VivianKuKu/CASA0021_Group-Prototype_Thinking-Scents/flutterBleV7/arduino_secrets.h

// This is the header file to store the wifi config

#ifndef _ARDUINO_SECRETS_H    // Put these two lines at the top of your file.
#define _ARDUINO_SECRETS_H  // (Use a suitable name, usually based on the file name.)

// Place your main header code here.
//please enter your sensitive data in the Secret tab/arduino_secrets.h

//
//#define SECRET_SSID "McDonald"
//#define SECRET_PASS "KFCyyds12138"
//#define SECRET_MQTTUSER "student"
//#define SECRET_MQTTPASS "ce2021-mqtt-forget-whale"


// #define SECRET_SSID "Burger-King"
// #define SECRET_PASS "!Haodepeiyongjun"
// #define SECRET_MQTTUSER "student"
// #define SECRET_MQTTPASS "ce2021-mqtt-forget-whale"

 #define SECRET_SSID "CE-Hub-Student"
 #define SECRET_PASS "casa-ce-gagarin-public-service"
 #define SECRET_MQTTUSER "student"
 #define SECRET_MQTTPASS "ce2021-mqtt-forget-whale"


//
// #define SECRET_SSID "50BD Hyperoptic Fibre Broadband"
// #define SECRET_PASS "neJRb22P9Unt"
// #define SECRET_MQTTUSER "student"
// #define SECRET_MQTTPASS "ce2021-mqtt-forget-whale"
#endif // _ARDUINO_SECRETS_H     // Put this line at the end of your file.
